palmelund/AT-AT---AuTomatic-Abstract-Typecaster/arduino/src/tasks.cpp

#include "tasks.h"

// -------------------------------
// Setup tasks
// -------------------------------
int32_t task_calibrate_ultra_sound_sensor(Ultra_Sound_Sensor *distance_sensor)
{
    int32_t min = distance_sensor_measure_distance(distance_sensor);
    int32_t current;
    for (uint8_t i = 0; i < CALIBRACTION_ITERATIONS - 1; ++i)
    {
        // We delay a little, because it seems that calling measure_distance
        // to rapidly, affects the results.
        delay(5);

        //DEBUG_PRINTLN_VAR(min);
        current = distance_sensor_measure_distance(distance_sensor);

        if (current < min)
            min = current;
    }

    return min - 8;
}

void task_calibrate_colors(int32_t *conveyor_target, Motor *conveyor,
                           SFE_ISL29125 *rgb_sensor, Delta_RGB colors[COLOR_COUNT])
{
    (*conveyor_target) = SEGMENT_DEGREE_LENGTH;

    DEBUG_PRINTLN("Calibrating colors...");
    for (uint8_t i = 0; i < COLOR_COUNT; ++i)
    {
        // Read samples to calibrate from
        RGB samples[CALIBRACTION_ITERATIONS];
        for (uint8_t i = 0; i < CALIBRACTION_ITERATIONS; ++i)
        {
            read_color(rgb_sensor, &samples[i]);
            //DEBUG_PRINT_RGB(samples[i]);
        }

        determin_bounding_sphere(samples, CALIBRACTION_ITERATIONS, &colors[i]);
        colors[i].delta += 100;

        DEBUG_PRINT_VAR(colors[i].delta);
        DEBUG_PRINT(" - ");
        DEBUG_PRINT_RGB(colors[i].rgb);

        while (motor_get_degrees(conveyor) < (*conveyor_target))
            ;
        (*conveyor_target) += SEGMENT_DEGREE_LENGTH;
    }

    DEBUG_PRINTLN("Done!");
}

// -------------------------------
// Task that are executed by the cyclic executive
// -------------------------------
void task_check_first_segment(Segment_Queue *segment_queue)
{
    Segment *first_segment = queue_next(segment_queue);

    // Tell the computer to take a picture
    Message take_picture_message;
    take_picture_message.type = MESSAGE_TYPE_COMMAND;
    take_picture_message.command.type = MESSAGE_COMMAND_TAKE_PICURE;

    io_send_message(&take_picture_message);

    // TODO: Computer will probably send both color and shape. Make it work!
    Message response;
    io_await_message(&response);

    first_segment->object_type = response.object.type;
    first_segment->color = response.object.color;
}

void task_determin_color(SFE_ISL29125 *color_sensor,
                         Segment_Queue *segment_queue, Delta_RGB known_colors[COLOR_COUNT])
{
    Segment *segment = get_segment(segment_queue, COLOR_SENSOR_SEGMENT_INDEX);

    if (segment->object_type == BALL)
    {
        const uint8_t result_count = COLOR_COUNT + 1;
        int8_t results[result_count] = {0, 0, 0, 0, 0};

        DEBUG_PRINTLN("B");
        for (uint8_t i = 0; i < SENSOR_PINGS; ++i)
        {
            RGB color;
            read_color(color_sensor, &color);
            results[determin_color(known_colors, &color)] += 1;
        }
        DEBUG_PRINTLN("E");

        uint8_t determined_color;
        int8_t max = -1;
        for (uint8_t i = 0; i < result_count; ++i)
        {
            if (results[i] > max)
            {
                max = results[i];
                determined_color = i;
            }
        }

        segment->color = determined_color;

        DEBUG_PRINT("C: ");
        DEBUG_PRINTLN(get_color_name(determined_color));
    }
}

void task_feed_ball(Motor *feeder)
{
    static uint8_t feed_counter = FEEDER_ITERATION;
    static int16_t deg = FEEDER_START_DEGREES + FEEDER_DEGREES;

    // We only feed a ball every x iterations
    if (feed_counter == FEEDER_ITERATION)
    {
        bool turn_status = motor_turn_to_degree(feeder, deg);

        ASSERT(turn_status);

        deg += FEEDER_DEGREES;
        if (deg == FEEDER_MAX_DEGREES)
            deg = FEEDER_START_DEGREES;

        feed_counter = 0;
    }

    feed_counter++;
}

void task_rotate_seperator(Advanced_Motor *separator, Segment_Queue *queue)
{
    static uint8_t last_position = UNKNOWN;
    static int16_t bucket_position[BUCKET_COUNT] = {
        RED_BUCKET,
        GREEN_BUCKET,
        BLUE_BUCKET,
        YELLOW_BUCKET,
        GARBAGE_BUCKET
    };

    Segment *segment = get_segment(queue, LAST_INDEX);
    uint8_t position;

    if (segment->object_type == BALL)
    {
        position = segment->color;
    }
    else
    {
        position = UNKNOWN;
    }

    if (position != last_position)
    {
        DEBUG_PRINTLN_VAR(bucket_position[position]);
        advanced_motor_turn_to_degree(separator, bucket_position[position]);
        last_position = position;
    }
}

/*

void task_send_take_picture(Segment_Queue *queue)
{
    Segment *segment = get_segment(queue, KINECT_SEGMENT_INDEX);
    if (segment->is_occupied)
    {
        Message message;
        message.type = MESSAGE_TYPE_COMMAND;
        message.command.type = MESSAGE_COMMAND_TAKE_PICURE;

        io_send_message(&message);
    }
}

void task_request_object_info(Segment_Queue *segment_queue)
{
    Segment *segment = get_segment(segment_queue, KINECT_SEGMENT_INDEX);
    if (segment->is_occupied)
    {
        Message message;
        io_await_message(&message);

        if (message.type == MESSAGE_TYPE_OBJECT)
        {
            Segment *segment =
                get_segment(segment_queue, KINECT_SEGMENT_INDEX);

            segment->object_type = message.object.type;
            return;
        }
    }
    else
    {
        return;
    }

    ASSERT(false);
}
*/
