palmelund/AT-AT---AuTomatic-Abstract-Typecaster/arduino/src/segments.cpp

#include "segments.h"

Segment* queue_next(Segment_Queue *segment_queue)
{
    segment_queue->index -= 1;
    if (segment_queue->index < 0)
        segment_queue->index = LAST_INDEX;

    return &segment_queue->data[segment_queue->index];
}

Segment* get_segment(Segment_Queue *segment_queue, uint8_t offset)
{
    return &segment_queue->data[(segment_queue->index + offset) % QUEUE_SIZE];
}
