palmelund/AT-AT---AuTomatic-Abstract-Typecaster/test/worst_case_execution_time/worst_case_execution_time.cpp

#include "worst_case_execution_time.h"

void wce_task_check_first_segment(Motor* conveyor, Motor* feeder,
    Advanced_Motor* seperator, Ultra_Sound_Sensor* distance_sensor,
    uint16_t distance_to_wall, Segment_Queue* segment_queue)
{
    Serial.println("wce_task_check_first_segment");
    motor_turn(conveyor);
    motor_turn(feeder);
    advanced_motor_turn(seperator, FORWARD);

    delay(1000);

    uint32_t time_start, time_end;
    for (uint8_t i = 0; i < CALIBRACTION_ITERATIONS; ++i)
    {
        time_start = micros();

        //task_check_first_segment(segment_queue);

        time_end = micros();

        Serial.print(i);
        Serial.print("\t& ");
        Serial.print(time_end - time_start);
        Serial.println("\t\\\\ \\hline");

        delay(100);
    }

    motor_stop(conveyor);
    motor_stop(feeder);
    advanced_motor_stop(seperator);
}

void wce_determin_color(Motor* conveyor, Motor* feeder,
    Advanced_Motor* seperator, SFE_ISL29125* color_sensor,
    Segment_Queue* segment_queue, Delta_RGB* known_colors)
{
    Serial.println("wce_determin_color");
    motor_turn(conveyor);
    motor_turn(feeder);
    advanced_motor_turn(seperator, FORWARD);

    for (uint8_t j = 0; j < QUEUE_SIZE; ++j)
    {
        Segment* segment = get_segment(segment_queue, j);
        segment->object_type = BALL;
    }

    delay(1000);

    uint32_t time_start, time_end;
    for (uint8_t i = 0; i < CALIBRACTION_ITERATIONS; ++i)
    {
        time_start = micros();

        task_determin_color(color_sensor, segment_queue, known_colors);

        time_end = micros();

        Serial.print(i);
        Serial.print("\t& ");
        Serial.print(time_end - time_start);
        Serial.println("\t\\\\ \\hline");

        delay(100);
    }

    motor_stop(conveyor);
    motor_stop(feeder);
    advanced_motor_stop(seperator);
}

void wce_task_feed_ball(Motor* conveyor, Motor* feeder,
    Advanced_Motor* seperator)
{
    Serial.println("wce_task_feed_ball");
    feeder->base.degrees = 0;
    feeder->base.buffer = 0;
    motor_turn(conveyor);

    delay(1000);

    uint32_t time_start, time_end;
    for (uint8_t i = 0; i < CALIBRACTION_ITERATIONS; ++i)
    {
        time_start = micros();

        task_feed_ball(feeder);

        time_end = micros();

        Serial.print(i);
        Serial.print("\t& ");
        Serial.print(time_end - time_start);
        Serial.println("\t\\\\ \\hline");

        delay(1000);
    }

    motor_stop(conveyor);
    motor_stop(feeder);
}

//#define YELLOW_BUCKET 100
//#define RED_BUCKET 260
void wce_task_rotate_seperator(Motor* conveyor, Motor* feeder,
    Advanced_Motor* seperator, Segment_Queue* queue)
{
    Serial.println("wce_task_rotate_seperator");
    motor_turn(conveyor);
    motor_turn(feeder);
    //advanced_motor_turn(seperator, FORWARD);

    Segment* segment = get_segment(queue, LAST_INDEX);
    segment->object_type = BALL;
    segment->color = YELLOW;

    task_rotate_seperator(seperator, queue);

    delay(1000);

    uint32_t time_start, time_end;
    for (uint8_t i = 0; i < CALIBRACTION_ITERATIONS; ++i)
    {
        segment->color = i % 2 == 0 ? RED : YELLOW;

        time_start = micros();

        task_rotate_seperator(seperator, queue);

        time_end = micros();

        Serial.print(i);
        Serial.print("\t& ");
        Serial.print(time_end - time_start);
        Serial.println("\t\\\\ \\hline");

        delay(1000);
    }

    motor_stop(feeder);
    motor_stop(conveyor);
}

void wce_conveyor_segment_turn_speed(Motor* conveyor)
{
    Serial.println("wce_conveyor_segment_turn_speed");
    motor_turn(conveyor);
    delay(1000);

    uint32_t time_start, time_end;
    for (uint8_t i = 0; i < CALIBRACTION_ITERATIONS; ++i)
    {
        uint32_t goal = motor_get_degrees(conveyor) + SEGMENT_DEGREE_LENGTH;
        time_start = micros();
        
        while (motor_get_degrees(conveyor) < goal) ;

        time_end = micros();

        Serial.print(i);
        Serial.print("\t& ");
        Serial.print(time_end - time_start);
        Serial.println("\t\\\\ \\hline");

        delay(1000);
    }
}
